wahlencraft/AWAC02/src/usart.h

/* This is a header declaring the functions defined by assembly rutines in
 * usart.S. */

#ifndef USART_H_
#define USART_H_

extern void USART_init();
extern void USART_putchar(char c);

#endif // USART_H_H
